austinscreations/WT32-SC01_POE/Ethernet POE shield/PCB/pictures/WT32SC01-POE top.png

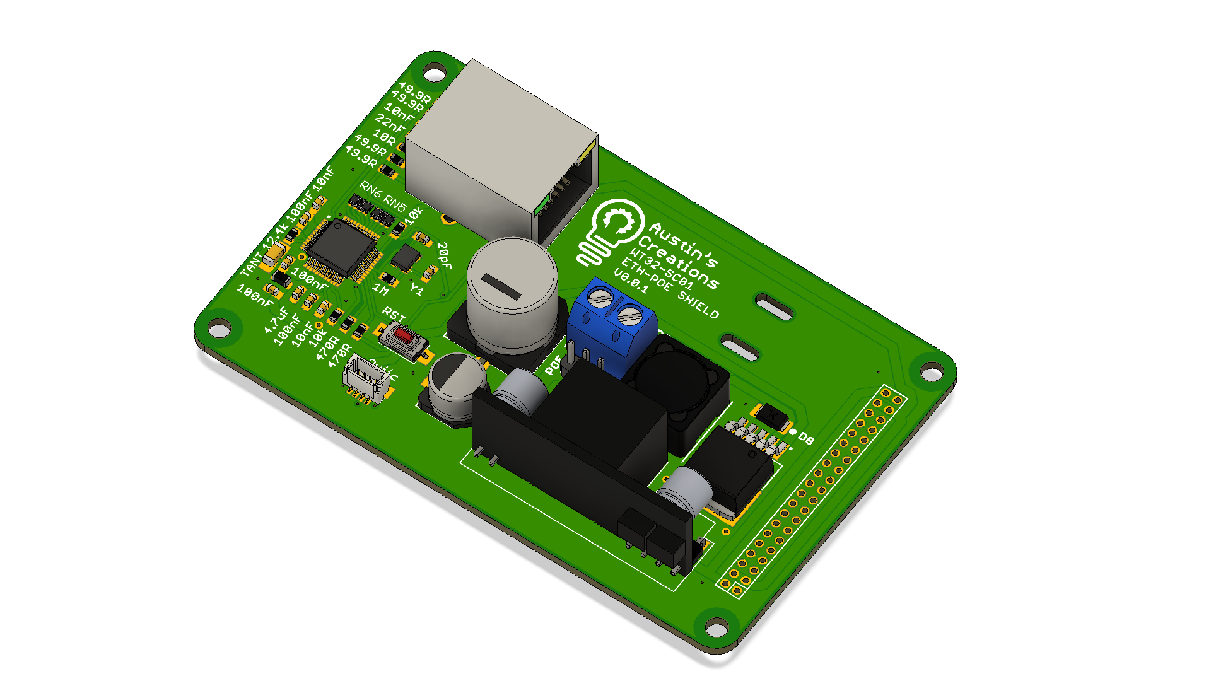
Ethernet POE shield/PCB/pictures/WT32SC01-POE top.png
